BoujeeEnjinia1701/snapframe/cad/drawings/SNF-DWG-001.pdf

CONCEPT, NOT FOR FABRICATION | SnapFrame · github.com/BoujeeEnjinia1701/snapframe

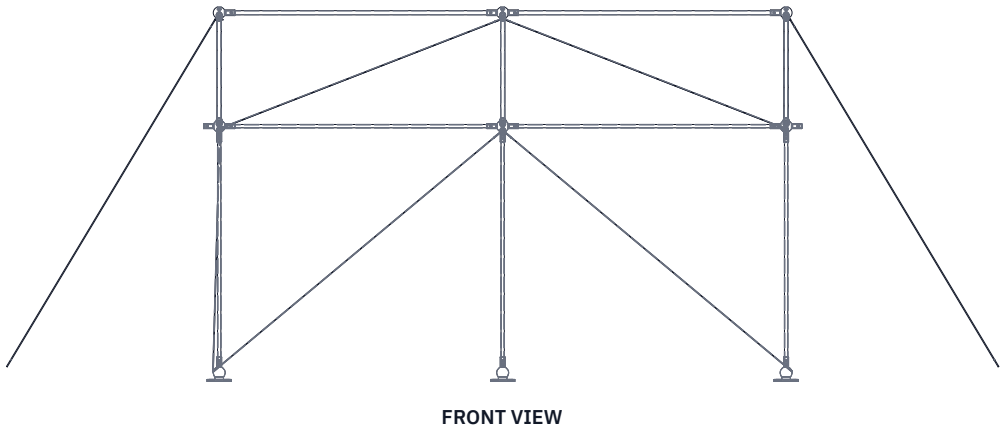
[picture p35: figure]
FRONT VIEW

Scale 1:50; looking at the front (along +Y)

TOP VIEW
Scale 1:50; looking down (along -Z)

RIGHT VIEW
Scale 1:50; looking at the right side (along -X)

7001

4170 2640

ISOMETRIC VIEW
Not to scale; seen from the front right and above, about 30 deg elevation

EAVE NODE, ALL SIX (6)
Detail, not to scale

RIDGE NODE, END (7)
Detail, not to scale

FOOT NODE (5)
Detail, not to scale

KEY DIMENSIONS AND DATA (SIZE M)
Floor 4.0 x 4.0 m, bays 2 x 2.0 m; eave 1.8 m, ridge 2.6 m (node centers)
Cut lengths: post 1650, rafter 2064, ridge and eave 1910 mm
Tubes: 1 in EMT rafters and ridge (OD 29.5 mm); 3/4 in EMT posts and eaves (OD 23.4 mm) Sockets: 65 mm engagement, bore = tube OD + 0.6 mm, wall 5 mm; core 84 mm
Button hole 6 mm at 40 mm from tube end, in a 16 mm finger recess; pin hole 8 mm at 15 mm
Foot plate 170 x 170 x 12 mm, two 18 mm anchor slots at 45 deg; anchor eye down on the plate Eave and ridge nodes: M10 cable bolt with spacer and 6 mm ring; cables clip to rings and anchor eyes Guy anchors 1.5 m beyond each gable; 10 brace cables, 4 mm
Wind rating 19.5 m/s at SF 1.5 (post governs, frame analysis); not rated for snow
Corner eave nodes: socket past the gable left blank and capped
Folding step (15) and two 560 mm rear anchors (16) not drawn
REV | DESCRIPTION | DATE | BY
P1 | Preliminary general arrangement (TRL 3) | 2026-09-25 | AC
P2 | 1 in ridge tubes; one eave node variant (DDR-002) | 2026-09-25 | AC
P3 | Layout and labels tidied | 2026-09-25 | AC
P4 | Design for construction (DDR-003): cable bolts, slots, pin | 2026-10-01 | AC
P5 | Folding step, long rear anchors, filled nylon nodes; 19.5 m/s (CAL v0.6) | 2026-10-02 | AC
SNAPFRAME | github.com/BoujeeEnjinia1701/snapframe

## General arrangement, size M

DRAWING NO.
SNF-DWG-001

REV
P5

SHEET
1 of 1

SIZE

## ANSI B

SCALE
1:50

UNITS
mm
PROJECTION | DATE
2026-10-02

DRAWN
Amish Chadha

MATERIAL / NOTES
EMT to ANSI C80.3; nodes printed in filled PA12-class nylon; see bom/bom.csv and SNF-CAL-001
Licensed CERN-OHL-S-2.0 · Design Molecule Lab · designmolecule.com | Generated from cad/src; do not edit by hand
