BoujeeEnjinia1701/snapframe/cad/drawings/SNF-DWG-101.pdf

### BUILD PLAN SKETCH, PLAN NOT YET BUILT SnapFrame · github.com/BoujeeEnjinia1701/snapframe

FRONT VIEW
Scale 1:5; looking at the front (along +Y)

TOP VIEW
Scale 1:5; looking down (along -Z)

RIGHT VIEW
Scale 1:5; looking at the right side (along -X)

170

170 170

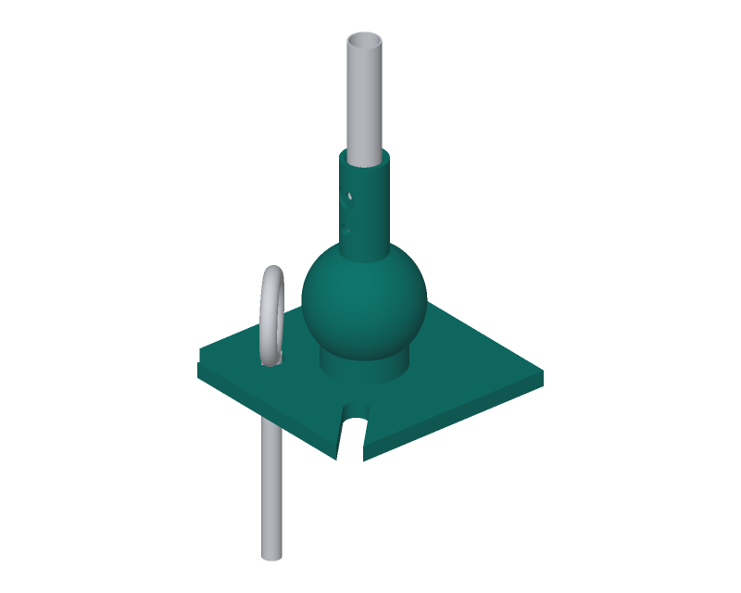
[picture p36: figure]

WHERE IT GOES
This part in colour, its neighbours in grey

HOW TO MAKE IT AND HOW IT FITS
Print 6, plate down on the bed; supports under the core only. Plate 170 x 170 x 12 mm; core 84 mm ball, its centre 60 mm up. One socket straight up: bore 24.0 mm, 65 mm deep to a flat stop; 1.5 mm chamfer at the mouth so the button rides in.
Button hole 6 mm, 85 mm above the core centre, on the outboard side, in a 16 mm finger recess with 1.5 mm of wall left.
Hitch pin hole 8 mm right through, 60 mm above the core centre, in line with the button hole.
Two anchor slots 18 mm wide at 45 degrees either side of the outboard side, round-ended 62 mm from the centre, open at the corners. The anchor uses the slot that points away from the shelter's middle (rear feet backward, front feet forward). Check: a post end slides in to the stop with the button pressed.
REV | DESCRIPTION | DATE | BY
P1 | Making sketch for the prototype build plan | 2026-10-02 | AC
SNAPFRAME | github.com/BoujeeEnjinia1701/snapframe

## SnapFrame foot node (make 6): making sketch

DRAWING NO.
SNF-DWG-101

REV
P1

SHEET
1 of 1

SIZE

## ANSI B

SCALE
1:5

UNITS
mm
PROJECTION | DATE
2026-10-02

DRAWN
Amish Chadha

MATERIAL / NOTES
Printed in filled PA12-class nylon, about 460 g
Licensed CERN-OHL-S-2.0 · Design Molecule Lab · designmolecule.com | Generated from cad/src; do not edit by hand
