BoujeeEnjinia1701/snapframe/cad/drawings/SNF-DWG-103.pdf

### BUILD PLAN SKETCH, PLAN NOT YET BUILT SnapFrame · github.com/BoujeeEnjinia1701/snapframe

FRONT VIEW
Scale 1:5; looking at the front (along +Y)

TOP VIEW
Scale 1:5; looking down (along -Z)

RIGHT VIEW
Scale 1:5; looking at the right side (along -X)

220

152 169

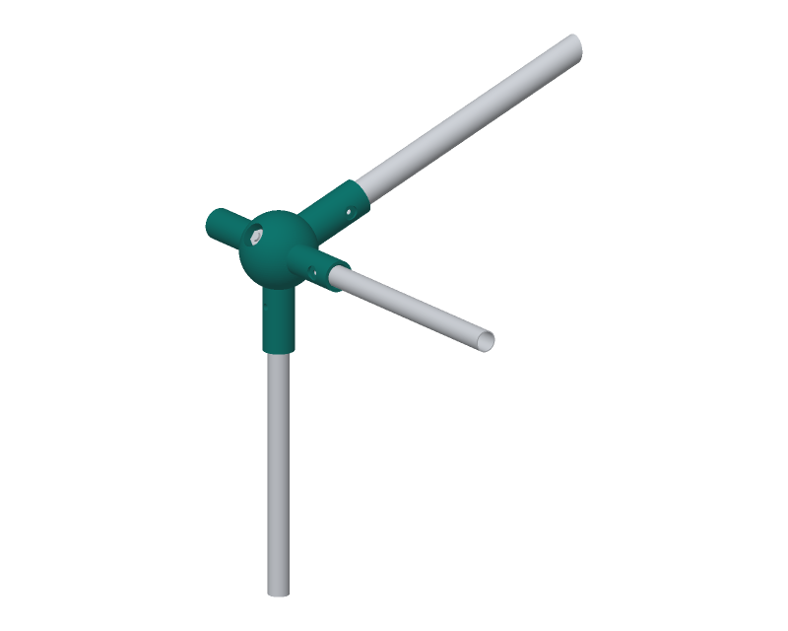
[picture p37: figure]

WHERE IT GOES
This part in colour, its neighbours in grey

HOW TO MAKE IT AND HOW IT FITS
Print 6, all the same. Four sockets from the 84 mm core:
post straight down (24.0 bore, hitch pin 60 mm from the centre); rafter inward and up 21.8 degrees (30.1 bore);
two eave tube sockets along the ridge line (24.0 bore).
Every bore 65 mm deep to a flat stop, 1.5 mm mouth chamfer, 6 mm button hole 85 mm out in a 16 mm finger recess.
Cable bolt hole 10.5 mm through the centre, pointing inward and 35 degrees down; flat spot face 39 mm out on that side, 27 mm nut recess on the far side, its floor 22 mm from the centre.
Fit: 30 mm washer, 14 x 10 mm spacer with the 6 mm ring on it, 24 mm washer, M10 x 90 bolt; 20 mm washer and nyloc nut in the recess. Snug plus a quarter turn: do not crush the print.
At the four corners the socket past the gable takes a cap.
REV | DESCRIPTION | DATE | BY
P1 | Making sketch for the prototype build plan | 2026-10-02 | AC
SNAPFRAME | github.com/BoujeeEnjinia1701/snapframe

## SnapFrame eave node (make 6): making sketch

DRAWING NO.
SNF-DWG-103

REV
P1

SHEET
1 of 1

SIZE

## ANSI B

SCALE
1:5

UNITS
mm
PROJECTION | DATE
2026-10-02

DRAWN
Amish Chadha

MATERIAL / NOTES
Printed in filled PA12-class nylon, about 287 g; M10 cable bolt set
Licensed CERN-OHL-S-2.0 · Design Molecule Lab · designmolecule.com | Generated from cad/src; do not edit by hand
