BoujeeEnjinia1701/snapframe/cad/drawings/SNF-DWG-105.pdf

### BUILD PLAN SKETCH, PLAN NOT YET BUILT SnapFrame · github.com/BoujeeEnjinia1701/snapframe

FRONT VIEW
Scale 1:5; looking at the front (along +Y)

TOP VIEW
Scale 1:5; looking down (along -Z)

RIGHT VIEW
Scale 1:5; looking at the right side (along -X)

152

219 100

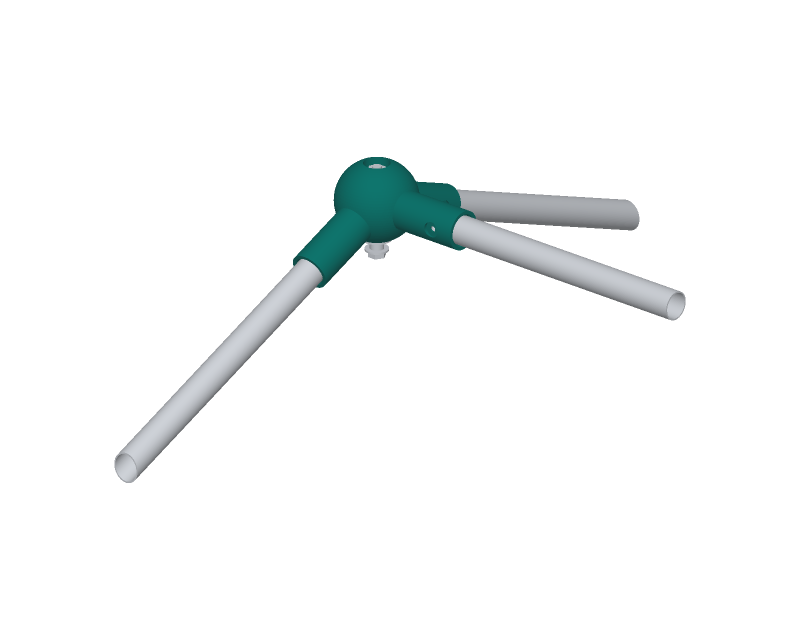
[picture p38: figure]

WHERE IT GOES
This part in colour, its neighbours in grey

HOW TO MAKE IT AND HOW IT FITS
Print 2, the same for the rear and the front (the front one is turned round). Three 30.1 mm sockets from the 84 mm core: two rafters, each 21.8 degrees below level, out to the sides; one ridge tube along the ridge line, toward the middle frame.
Bores 65 mm deep to a flat stop, 1.5 mm mouth chamfer, 6 mm button hole 85 mm out in a 16 mm finger recess.
Cable bolt hole 10.5 mm straight down through the centre: spot face on the underside, nut recess on top so nothing stands proud
under the roof tarpaulin.
Same bolt set as the eave node. The guy line ties to its ring.
Check: the ring swings freely on the spacer.
REV | DESCRIPTION | DATE | BY
P1 | Making sketch for the prototype build plan | 2026-10-02 | AC
SNAPFRAME | github.com/BoujeeEnjinia1701/snapframe

## SnapFrame ridge node, end (make 2): making sketch

DRAWING NO.
SNF-DWG-105

REV
P1

SHEET
1 of 1

SIZE

## ANSI B

SCALE
1:5

UNITS
mm
PROJECTION | DATE
2026-10-02

DRAWN
Amish Chadha

MATERIAL / NOTES
Printed in filled PA12-class nylon, about 277 g; M10 cable bolt set
Licensed CERN-OHL-S-2.0 · Design Molecule Lab · designmolecule.com | Generated from cad/src; do not edit by hand
