BoujeeEnjinia1701/snapframe/cad/drawings/SNF-DWG-106.pdf

### BUILD PLAN SKETCH, PLAN NOT YET BUILT SnapFrame · github.com/BoujeeEnjinia1701/snapframe

FRONT VIEW
Scale 1:5; looking at the front (along +Y)

TOP VIEW
Scale 1:5; looking down (along -Z)

RIGHT VIEW
Scale 1:5; looking at the right side (along -X)

220

219 100

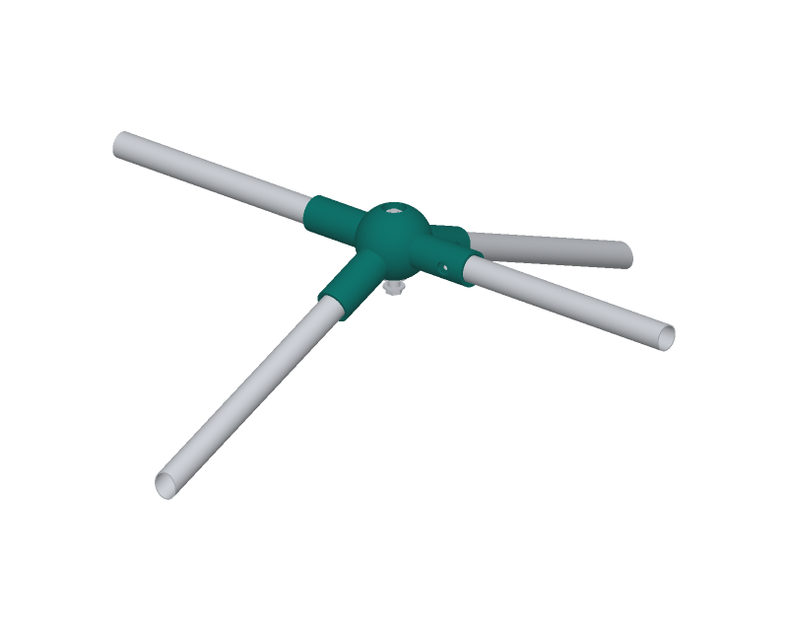
[picture p39: figure]

WHERE IT GOES
This part in colour, its neighbours in grey

HOW TO MAKE IT AND HOW IT FITS
Print 1. As the end ridge node with a fourth socket: two
30.1 mm ridge sockets, one each way along the ridge line. Bores 65 mm deep to a flat stop, 1.5 mm mouth chamfer, 6 mm button hole 85 mm out in a 16 mm finger recess.
Cable bolt straight down; the four roof cables clip to its ring. Print on its side with supports; the box is 220 x 219 x 99 mm, so the printer bed must be at least 230 mm.
Check: each ridge tube slides in to the stop with the button pressed, and the ring swings freely on the spacer.
REV | DESCRIPTION | DATE | BY
P1 | Making sketch for the prototype build plan | 2026-10-02 | AC
SNAPFRAME | github.com/BoujeeEnjinia1701/snapframe

## SnapFrame ridge node, middle (make 1): making sketch

DRAWING NO.
SNF-DWG-106

REV
P1

SHEET
1 of 1

SIZE

## ANSI B

SCALE
1:5

UNITS
mm
PROJECTION | DATE
2026-10-02

DRAWN
Amish Chadha

MATERIAL / NOTES
Printed in filled PA12-class nylon, about 304 g; M10 cable bolt set
Licensed CERN-OHL-S-2.0 · Design Molecule Lab · designmolecule.com | Generated from cad/src; do not edit by hand
