BoujeeEnjinia1701/snapframe/cad/drawings/SNF-DWG-102.pdf

### BUILD PLAN SKETCH, PLAN NOT YET BUILT SnapFrame · github.com/BoujeeEnjinia1701/snapframe

WHOLE TUBE, FRONT VIEW
Scale 1:10; looking at the front (along +Y)

1650

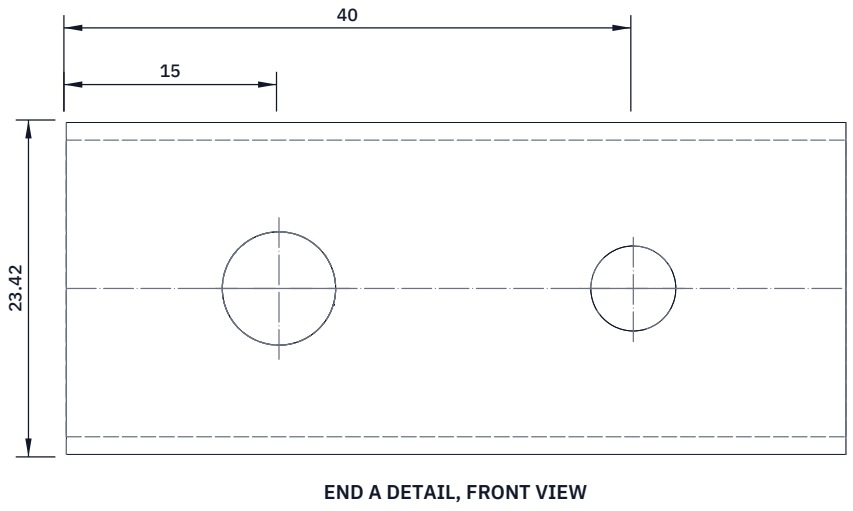
[picture p40: figure]
END A DETAIL, FRONT VIEW

Scale 2:1; button hole facing you

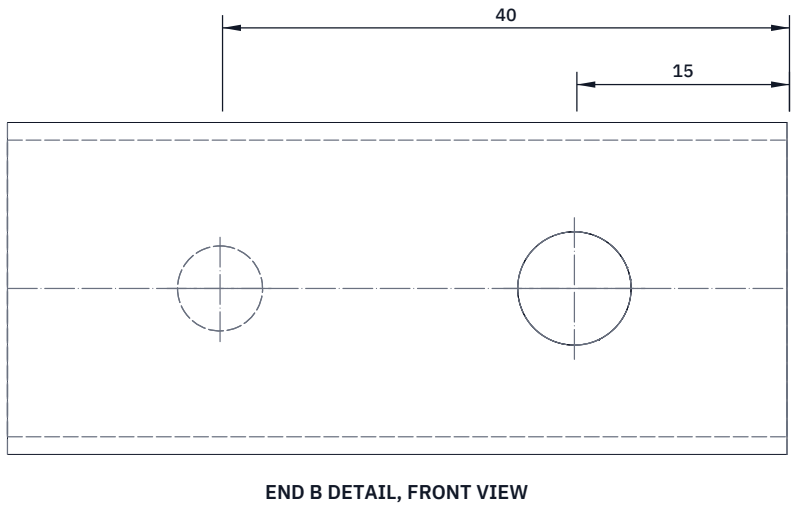
[picture p41: figure]
END B DETAIL, FRONT VIEW

Scale 2:1; button hole on the far side

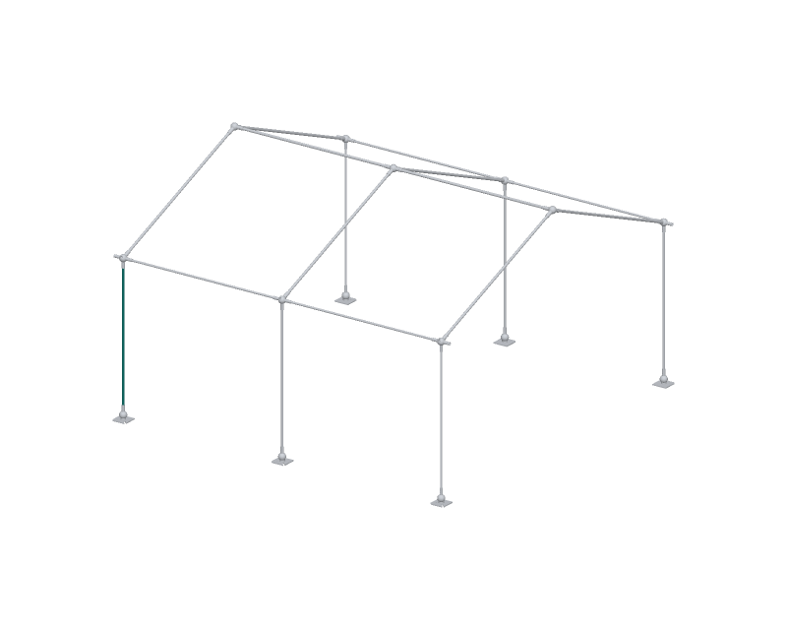
[picture p42: figure]

WHERE IT GOES
This part in colour, the rest of the frame in grey

HOW TO MAKE IT AND HOW IT FITS
Cut 6 lengths of 1650 mm from 3/4 in EMT.
Saw square (a pipe cutter or a fine blade); deburr inside
and out with a reamer and a file, and wipe clean.
Mark one line along the whole tube with a straight edge. Every hole is on that line: the button hole at end A on the line, the button hole at end B on the opposite side (turn the tube half a turn). Centre punch, drill 3 mm, then 6 mm for the button holes.
Hitch pin holes: 8 mm right through, 15 mm from each end, on the marked line (drill both walls in one pass in a vee block so the holes line up).
Paint a 40 mm colour band (post colour) at each end, starting 70 mm in, so it shows beside the socket mouth.
Push a 3/4 in snap button into each end, V spring first, until the button clicks into its 6 mm hole.
Check: the end slides into a socket to the stop and clicks.
REV | DESCRIPTION | DATE | BY
P1 | Making sketch for the prototype build plan | 2026-10-01 | AC
SNAPFRAME | github.com/BoujeeEnjinia1701/snapframe

## SnapFrame post (make 6): making sketch

DRAWING NO.
SNF-DWG-102

REV
P1

SHEET
1 of 1

SIZE

## ANSI B

SCALE
1:10, ends 2:1

UNITS
mm
PROJECTION | DATE
2026-10-01

DRAWN
Amish Chadha

MATERIAL / NOTES
3/4 in EMT, ANSI C80.3, OD 23.42 x 1.245 mm, one 3.05 m stick each
Licensed CERN-OHL-S-2.0 · Design Molecule Lab · designmolecule.com | Generated from cad/src; do not edit by hand
