BoujeeEnjinia1701/snapframe/cad/drawings/SNF-DWG-104.pdf

### BUILD PLAN SKETCH, PLAN NOT YET BUILT SnapFrame · github.com/BoujeeEnjinia1701/snapframe

WHOLE TUBE, FRONT VIEW
Scale 1:10; looking at the front (along +Y)

2064

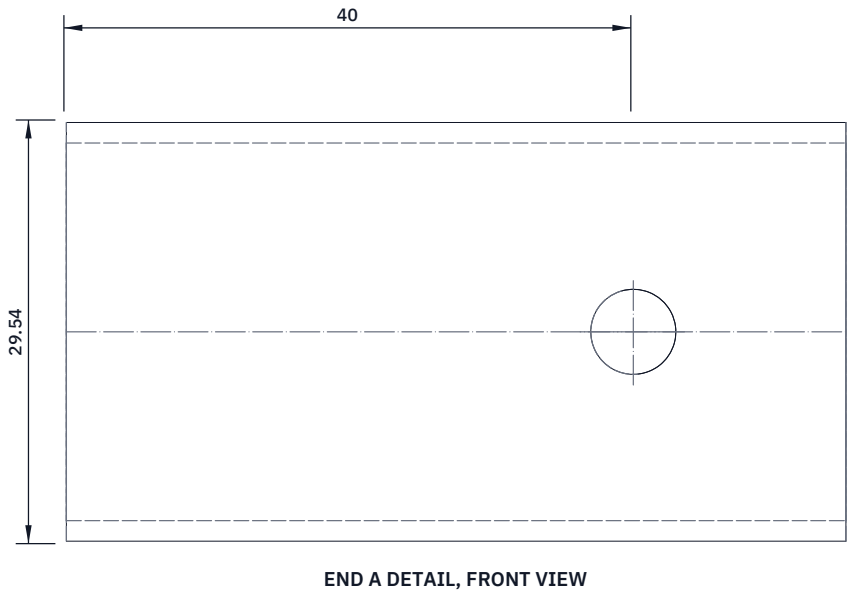
[picture p43: figure]
END A DETAIL, FRONT VIEW

Scale 2:1; button hole facing you

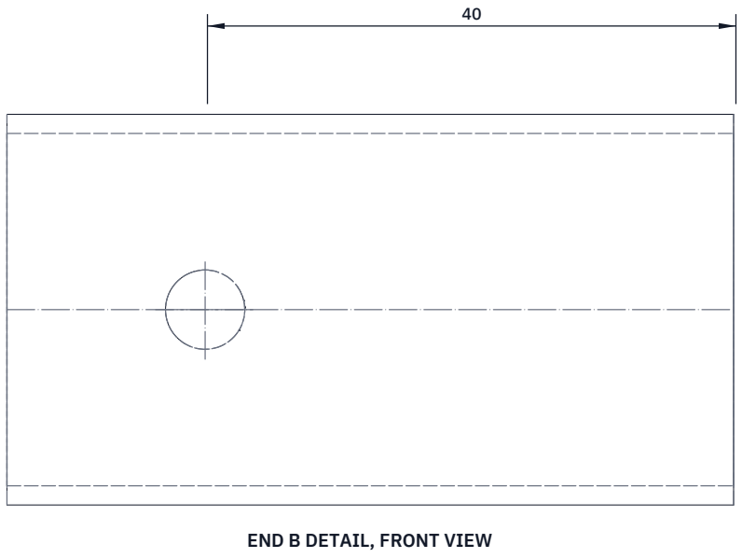
[picture p44: figure]
END B DETAIL, FRONT VIEW

Scale 2:1; button hole on the far side

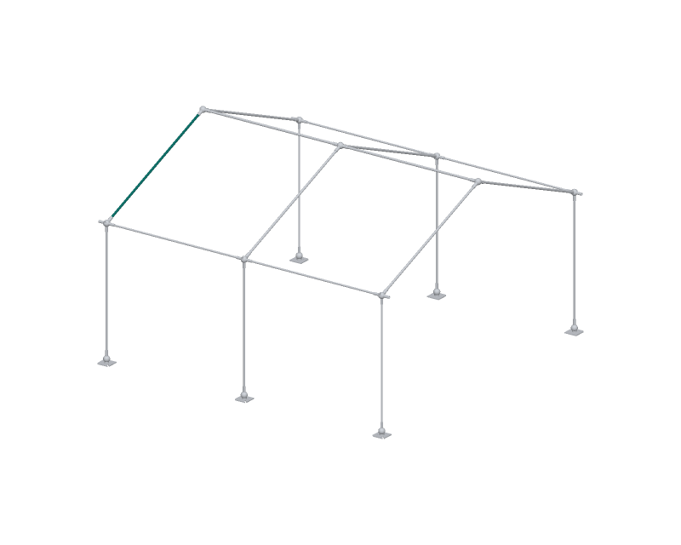
[picture p45: figure]

WHERE IT GOES
This part in colour, the rest of the frame in grey

HOW TO MAKE IT AND HOW IT FITS
Cut 6 lengths of 2064 mm from 1 in EMT.
Saw square (a pipe cutter or a fine blade); deburr inside
and out with a reamer and a file, and wipe clean.
Mark one line along the whole tube with a straight edge. Every hole is on that line: the button hole at end A on the line, the button hole at end B on the opposite side (turn the tube half a turn). Centre punch, drill 3 mm, then 6 mm for the button holes.
No hitch pin holes in the rafters.
Colour band (rafter colour) at each end, 70 mm in.
Fit a 1 in snap button in each end until it clicks.
Check: the end slides into an eave or ridge node socket to the stop and clicks; the other end's button faces the opposite way.
REV | DESCRIPTION | DATE | BY
P1 | Making sketch for the prototype build plan | 2026-10-01 | AC
SNAPFRAME | github.com/BoujeeEnjinia1701/snapframe

## SnapFrame rafter (make 6): making sketch

DRAWING NO.
SNF-DWG-104

REV
P1

SHEET
1 of 1

SIZE

## ANSI B

SCALE
1:10, ends 2:1

UNITS
mm
PROJECTION | DATE
2026-10-01

DRAWN
Amish Chadha

MATERIAL / NOTES
1 in EMT, ANSI C80.3, OD 29.54 x 1.448 mm, one 3.05 m stick each
Licensed CERN-OHL-S-2.0 · Design Molecule Lab · designmolecule.com | Generated from cad/src; do not edit by hand
