BoujeeEnjinia1701/snapframe/cad/drawings/SNF-DWG-107.pdf

### BUILD PLAN SKETCH, PLAN NOT YET BUILT SnapFrame · github.com/BoujeeEnjinia1701/snapframe

WHOLE TUBE, FRONT VIEW
Scale 1:10; looking at the front (along +Y)

1910

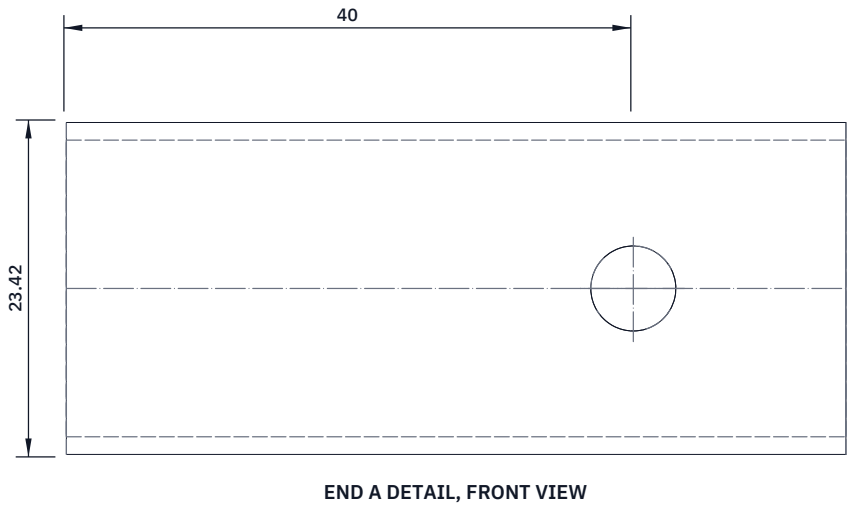
[picture p46: figure]
END A DETAIL, FRONT VIEW

Scale 2:1; button hole facing you

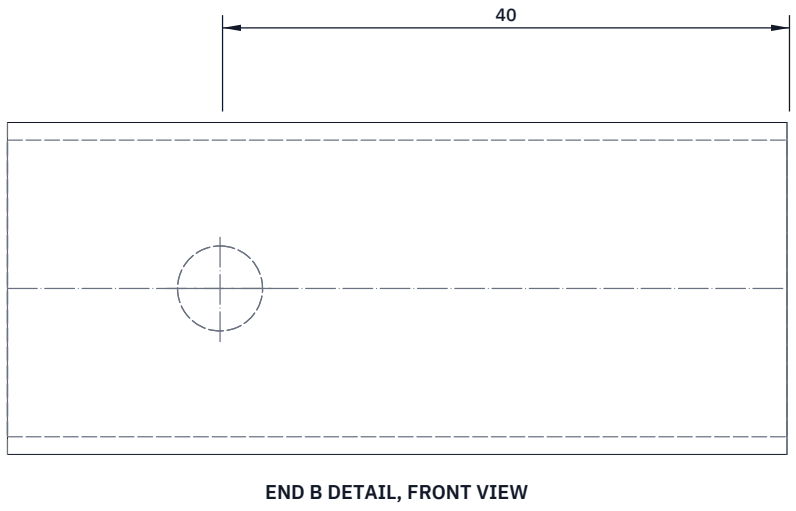
[picture p47: figure]
END B DETAIL, FRONT VIEW

Scale 2:1; button hole on the far side

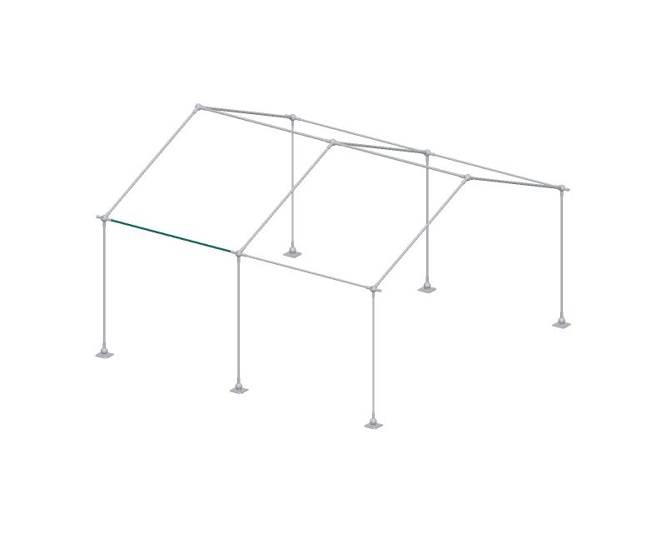
[picture p48: figure]

WHERE IT GOES
This part in colour, the rest of the frame in grey

HOW TO MAKE IT AND HOW IT FITS
Cut 4 lengths of 1910 mm from 3/4 in EMT.
Saw square (a pipe cutter or a fine blade); deburr inside
and out with a reamer and a file, and wipe clean.
Mark one line along the whole tube with a straight edge. Every hole is on that line: the button hole at end A on the line, the button hole at end B on the opposite side (turn the tube half a turn). Centre punch, drill 3 mm, then 6 mm for the button holes.
No hitch pin holes in the eave tubes.
Colour band (eave colour) at each end, 70 mm in; it tells them from the posts, which are the same tube.
Fit a 3/4 in snap button in each end until it clicks. Check: both ends click into eave node sockets.
REV | DESCRIPTION | DATE | BY
P1 | Making sketch for the prototype build plan | 2026-10-01 | AC
SNAPFRAME | github.com/BoujeeEnjinia1701/snapframe

## SnapFrame eave tube (make 4): making sketch

DRAWING NO.
SNF-DWG-107

REV
P1

SHEET
1 of 1

SIZE

## ANSI B

SCALE
1:10, ends 2:1

UNITS
mm
PROJECTION | DATE
2026-10-01

DRAWN
Amish Chadha

MATERIAL / NOTES
3/4 in EMT, ANSI C80.3, OD 23.42 x 1.245 mm, one 3.05 m stick each
Licensed CERN-OHL-S-2.0 · Design Molecule Lab · designmolecule.com | Generated from cad/src; do not edit by hand
