BoujeeEnjinia1701/snapframe/cad/drawings/SNF-DWG-109.pdf

### BUILD PLAN SKETCH, PLAN NOT YET BUILT SnapFrame · github.com/BoujeeEnjinia1701/snapframe

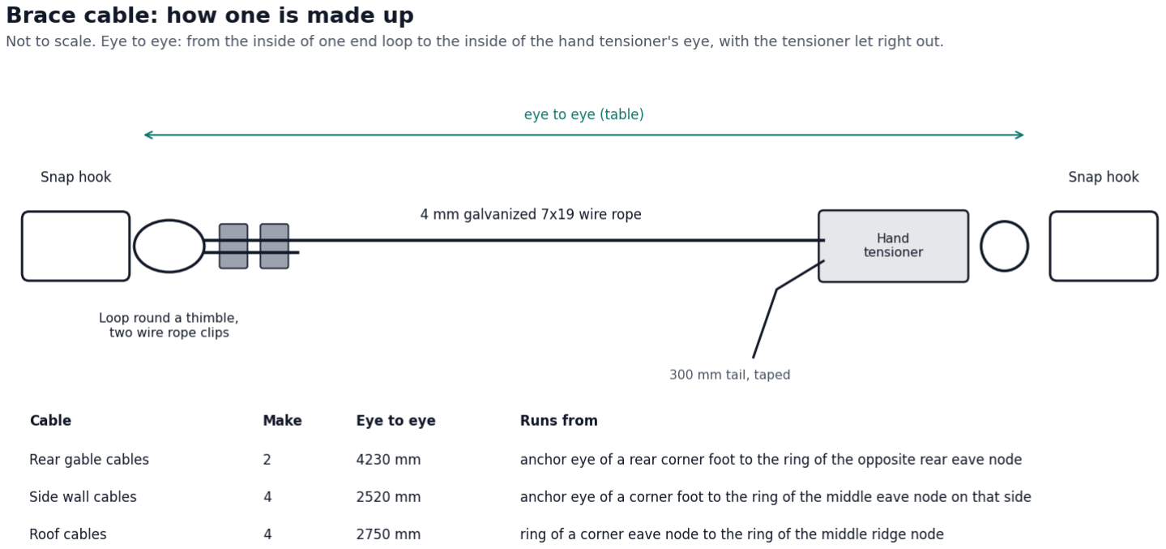
[picture p51: figure]

CABLE ASSEMBLY
Not to scale

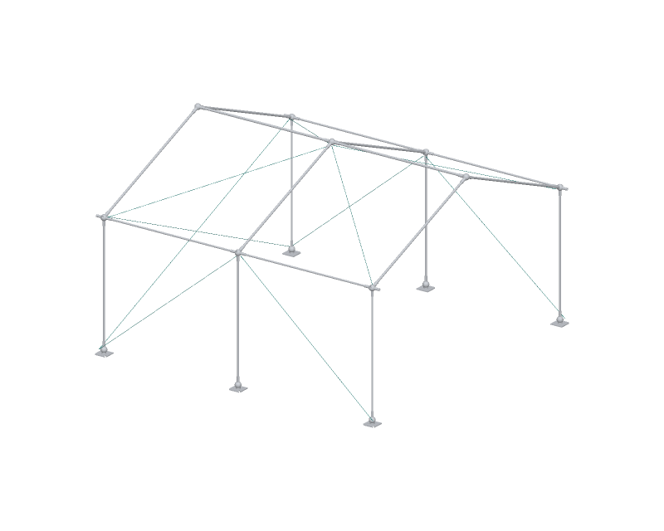
[picture p52: figure]

WHERE THEY GO
Cables in colour, the frame in grey

HOW TO MAKE THEM AND HOW THEY FIT
Cut the wire 700 mm longer than the eye to eye length (loop, tensioner and tail). Tape both ends before cutting.
End 1: loop the wire round a thimble and fit two wire rope clips, saddles on the long side, nuts torqued to the clip maker's figure. End 2: pass the wire through the hand tensioner as its maker shows. Clip a snap hook to the thimble and one to the tensioner's eye.
Set the length with the tensioner let out to the eye to eye length. Label each cable (gable, wall, roof) on a tag at end 1.
Fit: snap hooks clip to the anchor eyes at the feet and to the rings on the cable bolts; pull snug with the tensioner only. Check: each clip is tight after one pull of 300 N by hand scale.
REV | DESCRIPTION | DATE | BY
P1 | Making sketch for the prototype build plan | 2026-10-01 | AC
SNAPFRAME | github.com/BoujeeEnjinia1701/snapframe

## SnapFrame brace cables (make 10): making sketch

DRAWING NO.
SNF-DWG-109

REV
P1

SHEET
1 of 1

SIZE

## ANSI B

SCALE
1:1

UNITS
mm
PROJECTION | DATE
2026-10-01

DRAWN
Amish Chadha

MATERIAL / NOTES
4 mm galvanized 7x19 wire rope; thimbles, clips, snap hooks, hand tensioners
Licensed CERN-OHL-S-2.0 · Design Molecule Lab · designmolecule.com | Generated from cad/src; do not edit by hand
