BoujeeEnjinia1701/snapframe/cad/drawings/SNF-DWG-001.png

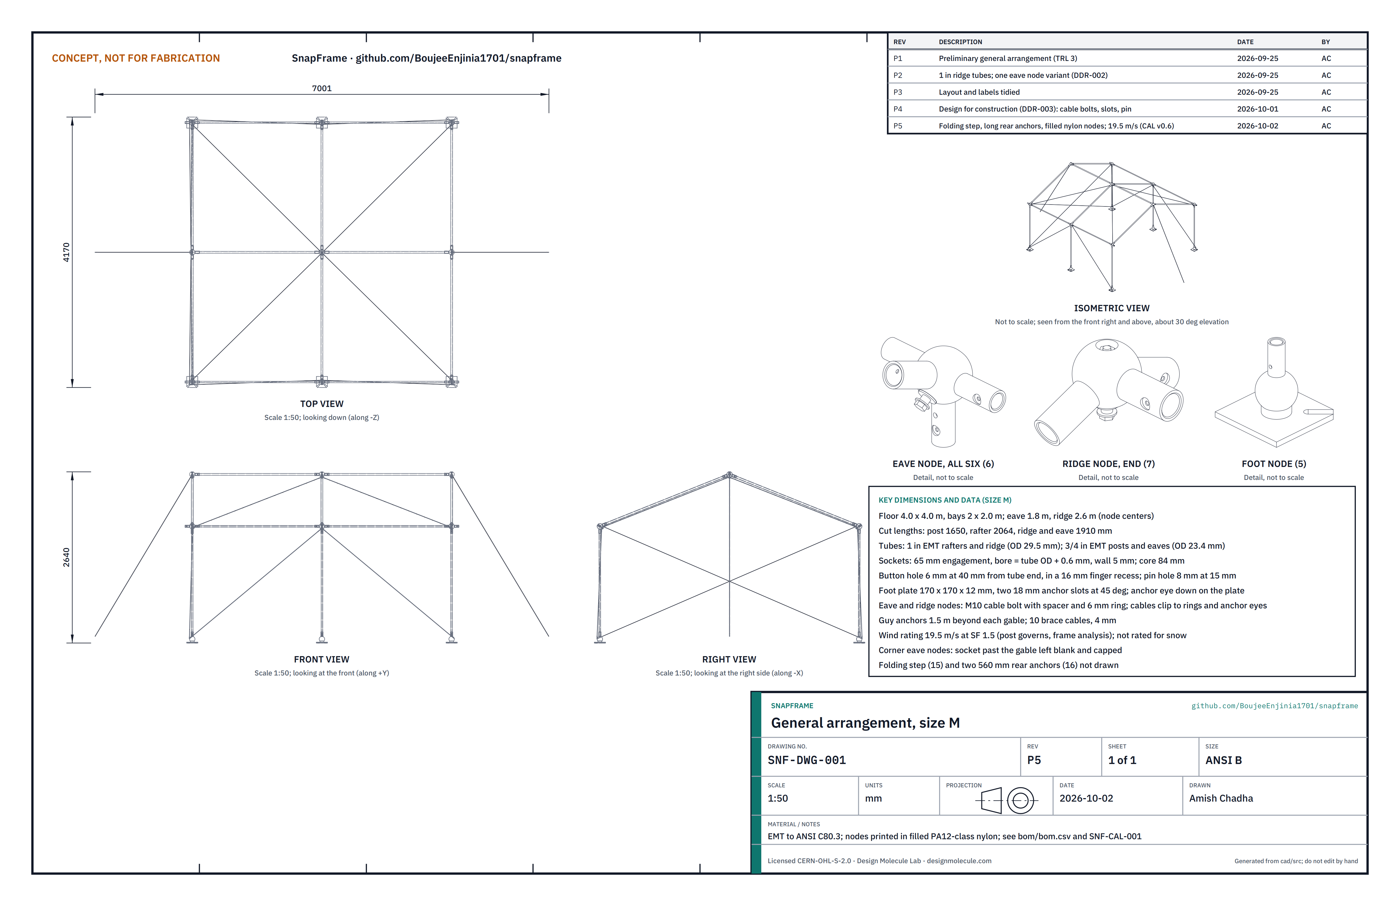
cad/drawings/SNF-DWG-001.png
