BoujeeEnjinia1701/snapframe/media/card.png

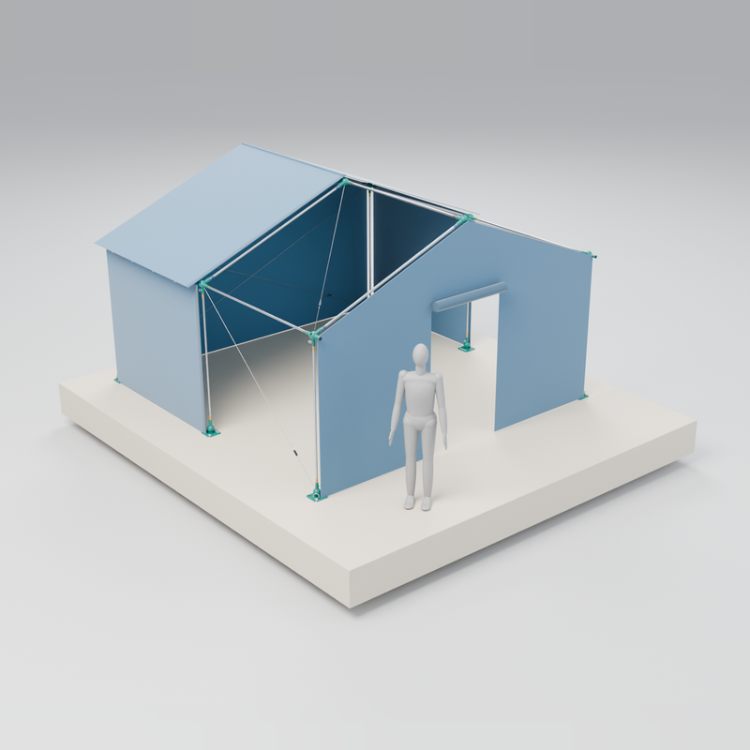
media/card.png
