BoujeeEnjinia1701/snapframe/media/render-detail.png

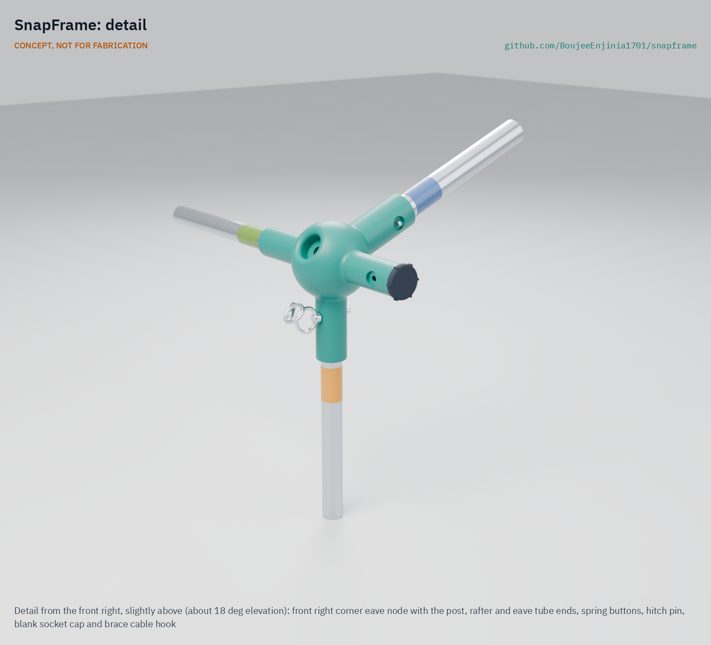
media/render-detail.png
