BoujeeEnjinia1701/snapframe/media/render-exploded.png

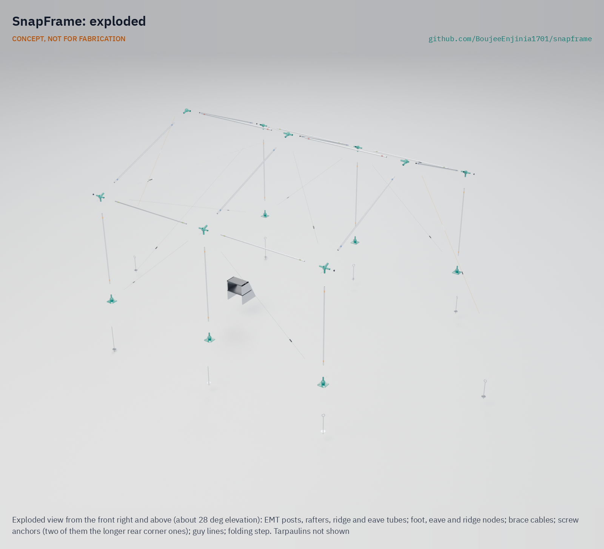
media/render-exploded.png
