BoujeeEnjinia1701/snapframe/media/social-preview.png

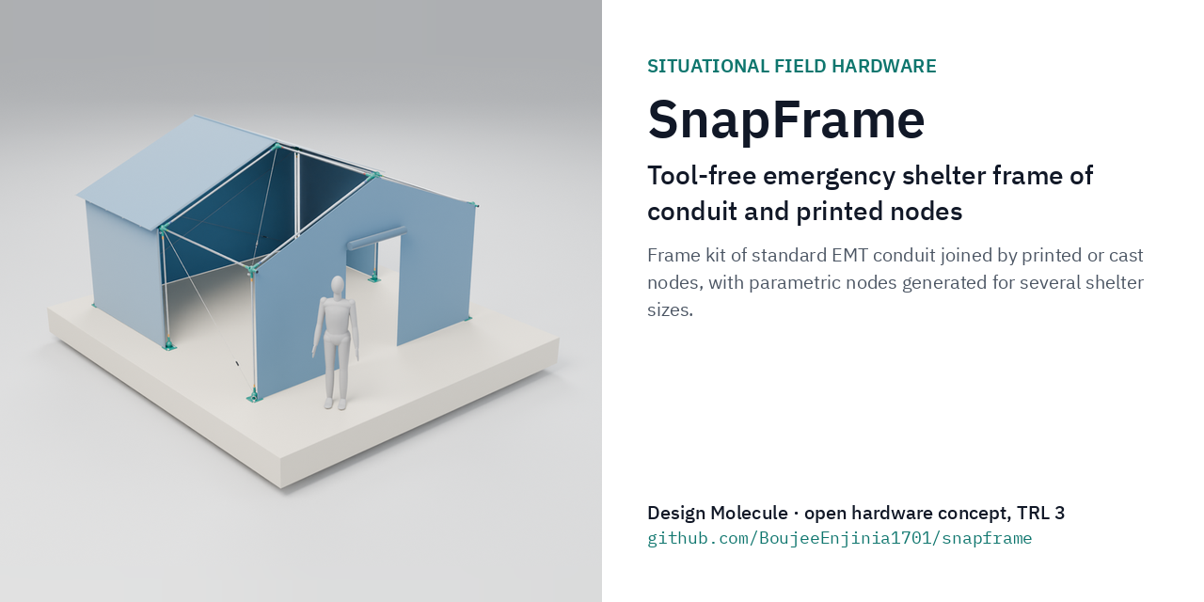
media/social-preview.png
